JayShoe/TEENSY_4.0_AUDIO_TOOLKIT/3d_models/teensy-4-0-1.snapshot.3/Teensy_4.0/Teensy_4.0_Decal/Teensy_4.0_Front.png

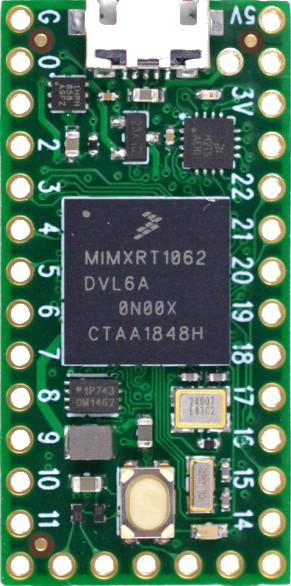
3d_models/teensy-4-0-1.snapshot.3/Teensy_4.0/Teensy_4.0_Decal/Teensy_4.0_Front.png
