JayShoe/TEENSY_4.0_AUDIO_TOOLKIT/documents/cs42448 part.PNG

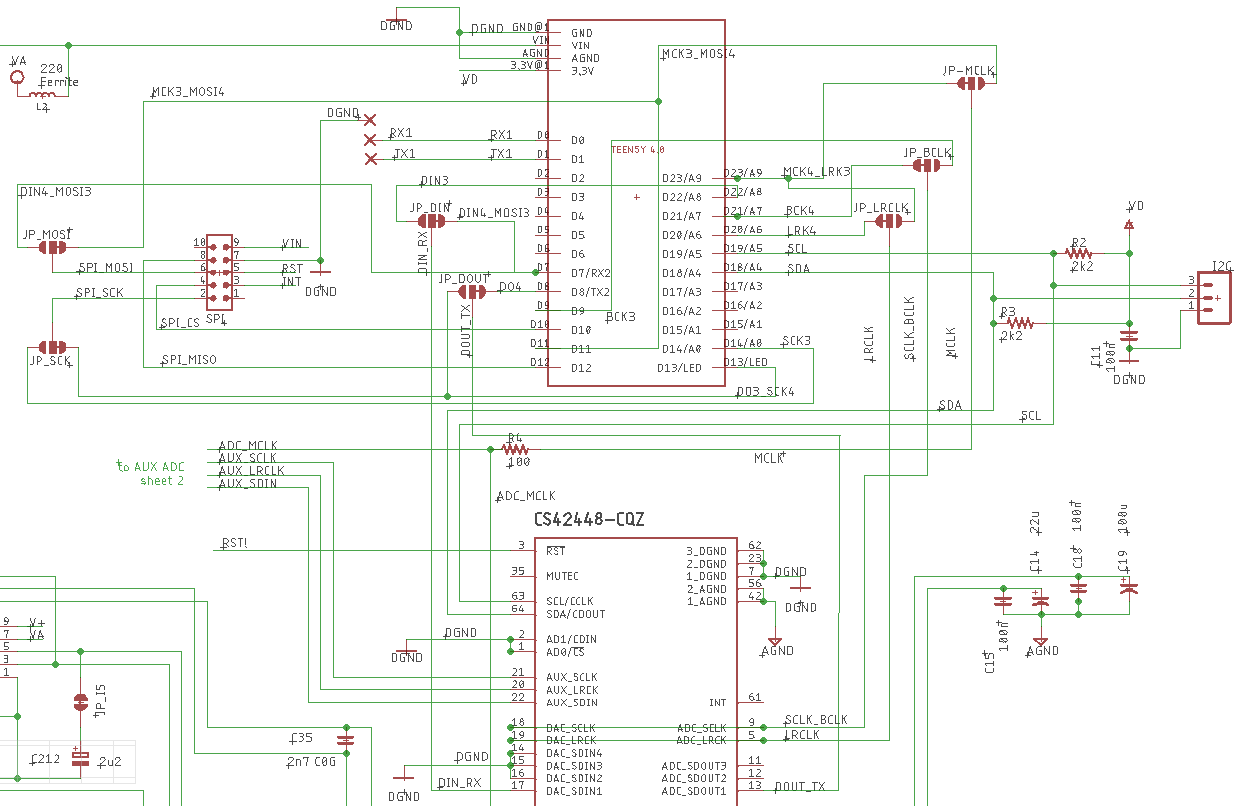
documents/cs42448 part.PNG
