JayShoe/TEENSY_4.0_AUDIO_TOOLKIT/3d_models/SPDIF_pjran1x1_Series.STEP

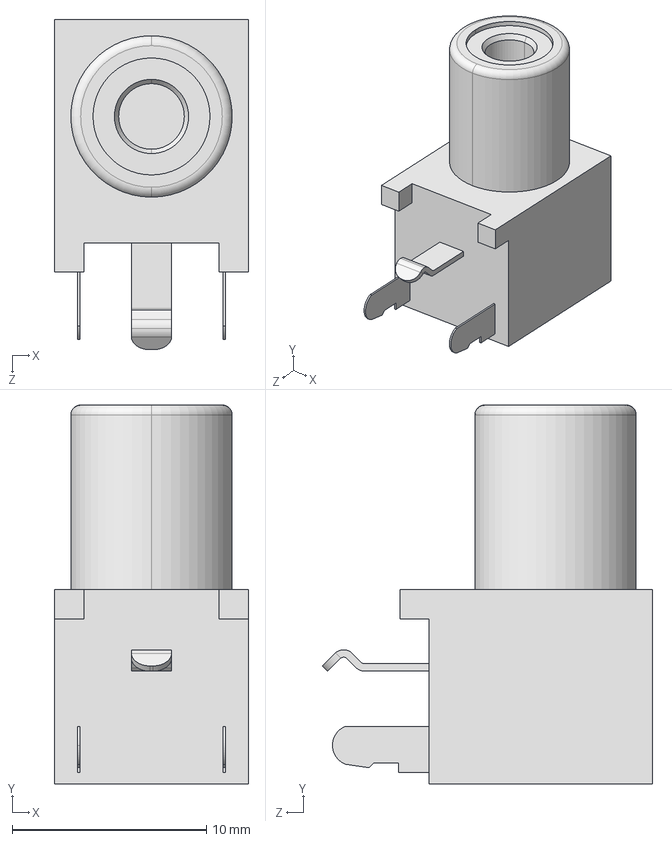
[picture p27: CAD file, 2020-04-11]
3d_models/SPDIF_pjran1x1_Series.STEP
10.00 x 19.5 x 17.0 mm
