JayShoe/TEENSY_4.0_AUDIO_TOOLKIT/3d_models/USB_A_c-292303-4-f-3d.stp

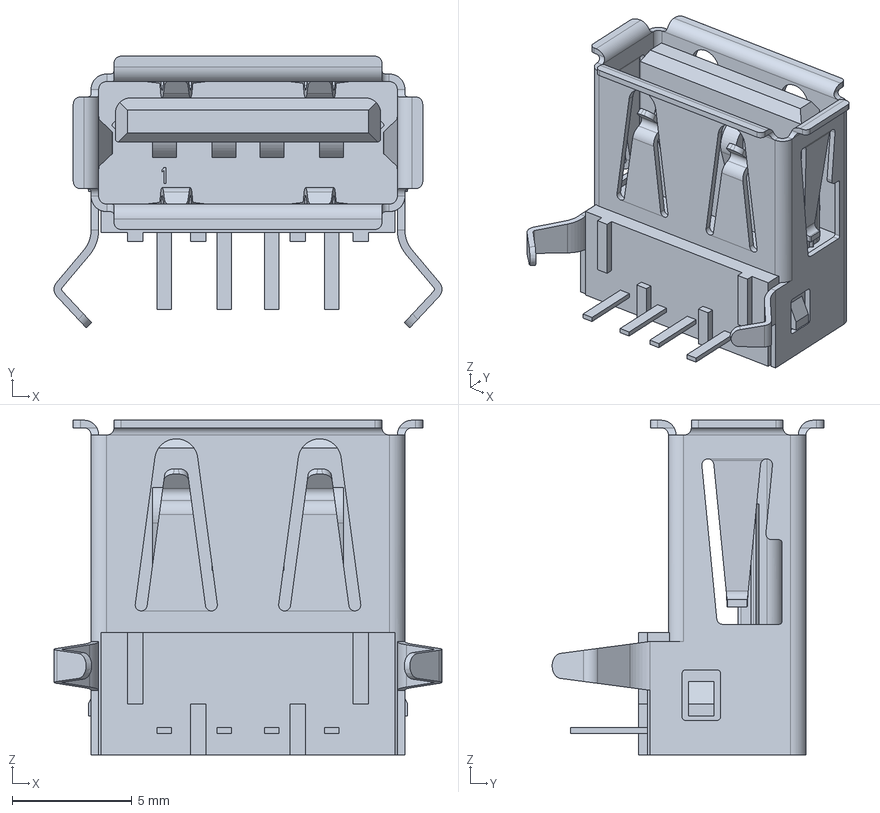
[picture p28: CAD file, 2020-04-11]
3d_models/USB_A_c-292303-4-f-3d.stp
16.2 x 11.4 x 14.0 mm
