JayShoe/TEENSY_4.0_AUDIO_TOOLKIT/3d_models/SOIC-14_3.9x8.7mm_P1.27mm.step

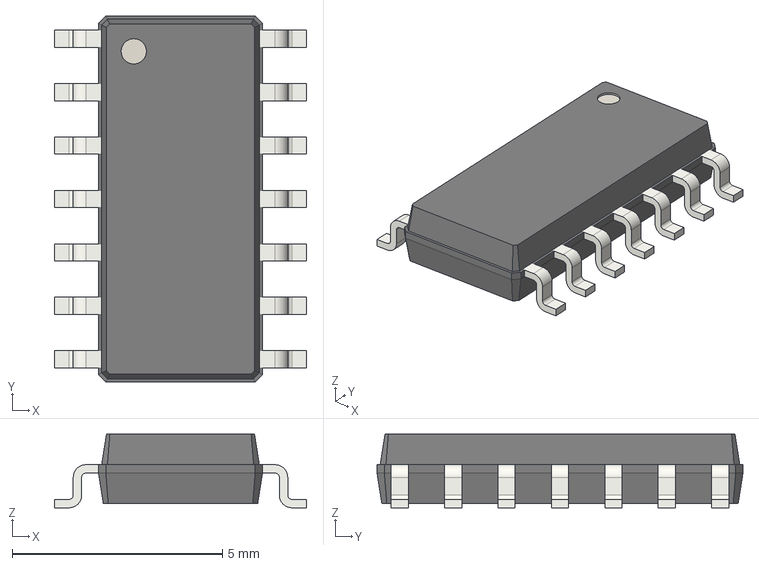
[picture p29: CAD file, 2020-04-11]
3d_models/SOIC-14_3.9x8.7mm_P1.27mm.step
6.00 x 8.70 x 1.75 mm
