JayShoe/TEENSY_4.0_AUDIO_TOOLKIT/3d_models/DC_BARREL_PJ-202AH.step

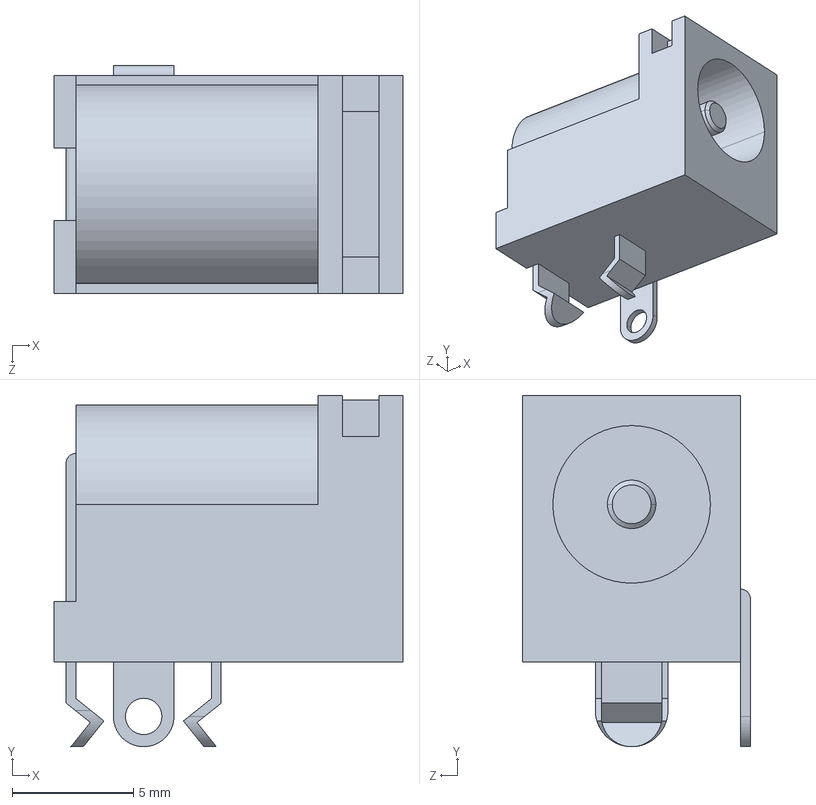
[picture p30: CAD file, 2020-04-11]
3d_models/DC_BARREL_PJ-202AH.step
14.4 x 14.5 x 9.40 mm
